stigsb/devais/docs/research/2026-09-13-mdbt50q.md

# Raytac MDBT50Q-1MV2 (nRF52840) — schematic research

Date: 2026-09-13. Every fact below is tagged VERIFIED (with source) or UNVERIFIED.

## Sources used

| Tag | Document | URL | Fetched |
|---|---|---|---|
| S1 | Raytac Approval Sheet, MDBT50Q-1MV2 & MDBT50Q-P1MV2, **Ver. L, 2023/05/24**, 73 pp (current version linked from Raytac's product page) | https://www.raytac.com/download/index.php?index_id=43 | yes (PDF downloaded, text + page images) |
| S2 | Same document, **Ver. K, 2022/07/01**, 75 pp (SparkFun mirror) | https://cdn.sparkfun.com/assets/4/7/4/3/8/_nRF52840__MDBT50Q-1MV2___MDBT50Q-P1MV2_Ver.K_spec.pdf | yes |
| S3 | Raytac product page MDBT50Q-1MV2 | https://www.raytac.com/product/ins.php?index_id=24 | yes |
| S4 | Nordic nRF52840 PS — Pin assignments | http://docs.nordicsemi.com/r/bundle/ps_nrf52840/page/pin.html | yes |
| S5 | Nordic nRF52840 PS — USBD | https://docs.nordicsemi.com/r/bundle/ps_nrf52840/page/usbd.html | yes |
| S6 | Nordic nRF52840 PS — SAADC | http://docs.nordicsemi.com/r/bundle/ps_nrf52840/page/saadc.html | yes |
| S7 | Nordic nRF52840 PS — UICR (REGOUT0) | http://docs.nordicsemi.com/r/bundle/ps_nrf52840/page/uicr.html | yes (enum values absent) |
| S8 | Nordic DevZone: "Resistors for D+ and D-?" | https://devzone.nordicsemi.com/f/nordic-q-a/94955/resistors-for-d-and-d- | yes |
| S9 | Nordic DevZone: "nRF52840 VDD output current maximum (Reg0 DCDC)" | https://devzone.nordicsemi.com/f/nordic-q-a/66975/nrf52840-vdd-output-current-maximum-reg0-dcdc | yes |
| S10 | Nordic DevZone: "nRF52840 Dongle Set REGOUT0 for 3V3 VDD OUT" | https://devzone.nordicsemi.com/f/nordic-q-a/84089/nrf52840-dongle-set-regout0-for-3v3-vdd-out | yes |
| S11 | Nordic SDK header `nrf52840_bitfields.h` (REGOUT0 enum), via sandeepmistry/arduino-nRF5 mirror of Nordic's SDK file | https://raw.githubusercontent.com/sandeepmistry/arduino-nRF5/master/cores/nRF5/SDK/components/device/nrf52840_bitfields.h | yes |
| S12 | Adafruit_nRF52_Bootloader repo | https://github.com/adafruit/Adafruit_nRF52_Bootloader | yes (via subagent) |

**Could not fetch:** Nordic PS `power.html` and `ref_circuitry.html` (WebFetch aborts: page exceeds 10 MB content limit). Nordic PS PDF direct download (`infocenter.nordicsemi.com/pdf/…`) returns HTTP 403. Mouser product pages (bot-detection block / 60 s timeout). Raytac "Footprint & Design Guide" ZIP (contains the recommended external 32.768 kHz spec) — not downloaded.

**Version note (VERIFIED, S1 vs S2):** I diffed the full §2.5 Pin Assignment text of Ver. K against Ver. L. They are byte-identical apart from page-number footers. The pad table below is current as of Ver. L.

---

## 1. Complete pad table — MDBT50Q-1MV2

VERIFIED, S1 §2.5 (pp. 14–17) / S2 §2.5 (pp. 16–18). 61 pads. Module 10.5 × 15.5 × 2.05 mm, 48 usable GPIO (S3).

**Legend:** `LF` = Raytac marks the pad "standard drive, low frequency I/O only". Raytac defines low-frequency I/O as **a signal with a frequency up to 10 kHz**, and states explicitly: **"SPI, I2C, UART, PWM are NOT low frequency I/O"** (S1 §2.6).

| Pad | Name | Function | Notes |
|---:|---|---|---|
| 1 | GND | Power | |
| 2 | GND | Power | |
| 3 | P1.10 | GPIO | **LF** |
| 4 | P1.11 | GPIO | **LF** |
| 5 | P1.12 | GPIO | **LF** |
| 6 | P1.13 | GPIO | **LF** |
| 7 | P1.14 | GPIO | **LF** |
| 8 | P1.15 | GPIO | **LF** |
| 9 | P0.03 / AIN1 | GPIO + analog in | **LF** |
| 10 | P0.29 / AIN5 | GPIO + analog in | **LF** |
| 11 | P0.02 / AIN0 | GPIO + analog in | **LF** |
| 12 | P0.31 / AIN7 | GPIO + analog in | **LF** |
| 13 | P0.28 / AIN4 | GPIO + analog in | **LF** |
| 14 | P0.30 / AIN6 | GPIO + analog in | **LF** |
| 15 | GND | Power | |
| 16 | P0.27 | GPIO | full-speed |
| 17 | P0.00 / XL1 | GPIO or 32.768 kHz crystal | |
| 18 | P0.01 / XL2 | GPIO or 32.768 kHz crystal | |
| 19 | P0.26 | GPIO | full-speed |
| 20 | P0.04 / AIN2 | GPIO + analog in | full-speed |
| 21 | P0.05 / AIN3 | GPIO + analog in | full-speed |
| 22 | P0.06 | GPIO | full-speed |
| 23 | P0.07 / TRACECLK | GPIO | full-speed |
| 24 | P0.08 | GPIO | full-speed |
| 25 | P1.08 | GPIO | full-speed |
| 26 | P1.09 / TRACEDATA3 | GPIO | full-speed |
| 27 | P0.11 / TRACEDATA2 | GPIO | full-speed |
| 28 | VDD | Power | supply in (normal mode) / REG0 output (high-voltage mode) |
| 29 | P0.12 / TRACEDATA1 | GPIO | full-speed |
| 30 | VDDH | Power | high-voltage supply |
| 31 | DCCH | Power | REG0 DC/DC converter output (external inductor) |
| 32 | VBUS | Power | 5 V input for the USB 3.3 V regulator |
| 33 | GND | Power | |
| 34 | D− | Digital I/O | USB D− |
| 35 | D+ | Digital I/O | USB D+ |
| 36 | P0.14 | GPIO | full-speed |
| 37 | P0.13 | GPIO | full-speed |
| 38 | P0.16 | GPIO | full-speed |
| 39 | P0.15 | GPIO | full-speed |
| 40 | P0.18 / nRESET | GPIO, configurable as system RESET | Raytac recommends QSPI/CSN |
| 41 | P0.17 | GPIO | full-speed |
| 42 | P0.19 | GPIO | Raytac recommends QSPI/SCK |
| 43 | P0.21 | GPIO | Raytac recommends QSPI |
| 44 | P0.20 | GPIO | full-speed |
| 45 | P0.23 | GPIO | Raytac recommends QSPI |
| 46 | P0.22 | GPIO | Raytac recommends QSPI |
| 47 | P1.00 / TRACEDATA0 | GPIO | Raytac recommends QSPI |
| 48 | P0.24 | GPIO | full-speed |
| 49 | P0.25 | GPIO | full-speed |
| 50 | P1.02 | GPIO | **LF** |
| 51 | SWDIO | Debug | SWD data |
| 52 | P0.09 / NFC1 | GPIO or NFC antenna | **LF** |
| 53 | SWDCLK | Debug | SWD clock |
| 54 | P0.10 / NFC2 | GPIO or NFC antenna | **LF** |
| 55 | GND | Power | |
| 56 | P1.04 | GPIO | **LF** |
| 57 | P1.06 | GPIO | **LF** |
| 58 | P1.07 | GPIO | **LF** |
| 59 | P1.05 | GPIO | **LF** |
| 60 | P1.03 | GPIO | **LF** |
| 61 | P1.01 | GPIO | **LF** |

### Raytac's LF list vs Nordic's LF list — they differ

- **Nordic** (VERIFIED, S4) marks exactly these aQFN73 pins "standard drive, low frequency I/O only": **P0.02, P0.03, P0.28, P0.29, P0.30, P0.31, P1.10, P1.11, P1.12, P1.13, P1.14, P1.15**. Same 10 kHz definition.
- **Raytac** (VERIFIED, S1 §2.5/§2.6) marks all of the above **plus P0.09, P0.10, P1.01, P1.02, P1.03, P1.04, P1.05, P1.06, P1.07**. §2.6 "GPIO Located Near the Radio" explains why: these sit next to the radio inside the module, and "wrong usage may lead to undesirable performance".

Treat Raytac's superset as binding for this module. Note that P1.08 and P1.09 (pads 25, 26) are **not** in either list, so they are full-speed on this module.

---

## 2. Review of the proposed pin allocation

**Result: every pad number is correct. Zero pad-number errors, zero non-GPIO pads, zero high-speed signals on low-frequency pads.**

| Signal | GPIO | Claimed pad | Pad table says | Verdict |
|---|---|---:|---|---|
| I2S BCLK | P0.26 | 19 | P0.26, full-speed | OK |
| I2S LRCLK | P0.27 | 16 | P0.27, full-speed | OK |
| I2S SDOUT | P0.08 | 24 | P0.08, full-speed | OK |
| PDM CLK | P0.06 | 22 | P0.06, full-speed | OK |
| PDM DATA | P0.07 | 23 | P0.07, full-speed | OK |
| PTT button | P0.02 | 11 | P0.02/AIN0, **LF** | OK — a button is DC, well under 10 kHz |
| PWR button | P0.03 | 9 | P0.03/AIN1, **LF** | OK — same |
| LED data (WS2812) | P0.11 | 27 | P0.11, full-speed | OK — 800 kHz needs a full-speed pad, and this is one |
| LED power enable | P0.12 | 29 | P0.12, full-speed | OK |
| Mic enable | P0.13 | 37 | P0.13, full-speed | OK |
| Amp enable | P0.14 | 36 | P0.14, full-speed | OK |
| Charger EN1 | P1.10 | 3 | P1.10, **LF** | OK — static enable |
| Charger EN2 | P1.11 | 4 | P1.11, **LF** | OK — static enable |
| Type-C status | P1.12 | 5 | P1.12, **LF** | OK if the signal is static/slow |
| Type-C status | P1.13 | 6 | P1.13, **LF** | OK if the signal is static/slow |
| Battery ADC | P0.04/AIN2 | 20 | P0.04/AIN2, full-speed | OK |
| RESET | P0.18 | 40 | P0.18/nRESET | OK |
| SWDIO | — | 51 | SWDIO | OK |
| SWDCLK | — | 53 | SWDCLK | OK |
| LF crystal XL1 | P0.00 | 17 | P0.00/XL1 | OK |
| LF crystal XL2 | P0.01 | 18 | P0.01/XL2 | OK |

### Issues that are not pad-number errors but affect the schematic

**A1 — Bootloader pin collision (VERIFIED, S12).** The stock Adafruit bootloader board `raytac_mdbt50q_db_40` (`UF2_BOARD_ID "nRF52840-MDBT50Q-1MV2"`) defines `BUTTON_DFU = P0.11` and `BUTTON_DFU_OTA = P0.12` — exactly your LED data and LED power-enable pins — and `LED_PRIMARY/SECONDARY/TERTIARY = P1.13/P1.14/P1.15`, of which P1.13 is your Type-C status pin. Using the stock board definition unmodified will fight your hardware at boot. Fork it into a custom board definition.

**A2 — P0.18 / nRESET is a plain GPIO on a blank part.** Pad 40 only behaves as a reset pin once UICR `PSELRESET[0]` and `PSELRESET[1]` are programmed to 18. Raised UICR bits need a page erase, i.e. SWD (see S10). Budget for that in the first flash.

**A3 — Battery ADC may be unnecessary.** If the design ends up in high-voltage mode (VDDH on the Li-ion rail), the SAADC `VDDHDIV5` input measures VDDH/5 internally with no external divider and no pin — freeing pad 20 (§6 below).

**A4 — Avoid the Raytac-only LF pads for anything fast.** P0.09, P0.10, P1.01–P1.07 and P1.02 are full-speed per Nordic but LF-only per Raytac. None are in your allocation; keep it that way.

**A5 — Unallocated but mandatory pads:** 1, 2, 15, 33, 55 (GND), 28 (VDD), 30 (VDDH), 31 (DCCH), 32 (VBUS), 34 (D−), 35 (D+). Covered in §3/§5.

---

## 3. USB pads and the normal-voltage-mode (VDD = VDDH = 3.3 V) reference circuit

Raytac §8.3 "Reg0 DC/DC and LDO Mode Disabled — Recommend using when the highest input voltage is less than 3.6 V" is the normal-voltage-mode circuit. VERIFIED, S1 p. 40 / S2 p. 42 (schematic image read at 400 dpi).

### Connections

| Pad | Net | Component |
|---:|---|---|
| 28 VDD | 3.3 V rail ("Normal Voltage input") | **C11 = 10 µF** to GND |
| 30 VDDH | **same 3.3 V rail** — tied directly to VDD | — |
| 31 DCCH | **not connected** | — |
| 32 VBUS | 5 V net | **C25 = 10 µF** to GND |
| 33, 15, 55, 1, 2 GND | GND | — |
| 34 D− | USB connector D− | **R30 = 27 Ω series** |
| 35 D+ | USB connector D+ | **R31 = 27 Ω series** |
| 17 XL1 / 18 XL2 | 32.768 kHz crystal X2 | **C12 = C13 = 12 pF**, marked *Optional* |
| 52 P0.09/NFC1, 54 P0.10/NFC2 | NFC loop | C19, C21 — **omit** if NFC unused |

Nordic confirms the mode: normal voltage mode is entered when the supply is connected to **both** VDD and VDDH (pins shorted); REG0 is then automatically bypassed and only REG1 runs.

### Series resistors on D+/D− — Raytac and Nordic disagree

- **Raytac (VERIFIED, S1 §8.3/§8.4):** shows **27 Ω in series on both D+ and D−** in every USB reference circuit.
- **Nordic (VERIFIED, S8):** Nordic employee, verbatim — *"The external series resistors are not required for D+ and D-. They are already built into the USB PHY."* A related thread notes the older DK's 39 Ω resistors were legacy and would be removed from future DKs.

Practical resolution: lay out **0 Ω / DNP-able footprints** on D+/D− so you can populate 0 Ω (Nordic-correct) and still fall back to Raytac's 27 Ω without a respin. Do not stack 27 Ω on top of the PHY's own series termination if you want a compliant eye.

### VBUS

- **5 V goes directly to pad 32.** No regulator, no divider. VBUS operating range **4.35 / 5.0 / 5.5 V** (min/nom/max); absolute max 5.8 V (VERIFIED, S1 §5.1/§5.2, reproduced from nRF52840 PS v1.7).
- The nRF52840 has a dedicated internal regulator converting VBUS to the 3.3 V used by the USB signalling interface, so **both VBUS and VDD (or VDDH) must be supplied for USB to work** (VERIFIED, S5).
- The **1.5 kΩ D+ pull-up is on-chip and software-controlled** (`USBPULLUP`). Nordic: *"This forbids the use of an external pull-up."* (VERIFIED, S5). Do not fit one.
- D+/D− are **not 5 V tolerant** (VERIFIED, S5). Nordic specifies no external components on them; ESD diodes are optional and your own call.
- Raytac's §8.5 "USB Disabled": **leave D+ and D− as NC** when USB is unused (VERIFIED, S1).
- Raytac's USB circuits show **C25 = 10 µF on VBUS**. UNVERIFIED whether Nordic mandates a specific VBUS cap value (the PS ref-circuitry page could not be fetched).

### Decoupling that Raytac requires

Raytac's reference circuits show only these external passives on the power pads (VERIFIED, S1 §8.1–§8.4):

- **VDD (pad 28): 10 µF (C11).** Present in every circuit.
- **VDDH (pad 30): 10 µF (C24).** Only in the high-voltage circuits; in normal mode VDDH is just tied to VDD and shares C11.
- **VBUS (pad 32): 10 µF (C25).**
- **DCCH (pad 31): 10 µH inductor (L4) to VDDH**, only when REG0 DC/DC is enabled. Raytac's spec: *"Recommended L4 spec: 10 µH, 0603 Chip Inductor, IDC,min = 80 mA, ±20%"*.
- **DEC1–DEC6 / DCC pins are not brought out** — they are inside the module and already decoupled. Nothing for you to fit.

Add your own 100 nF local bypass next to the module in addition to the bulk caps; Raytac does not show one but it costs nothing. (That last sentence is my recommendation, not a Raytac requirement.)

### What is already inside the module

VERIFIED, S1 §3 and the §8 preamble, verbatim: **"32 MHz crystal and RF (VDD) DC/DC inductor (Reg1) are already inside the module."** So:

- No external 32 MHz crystal or load caps.
- No external REG1 (DCC) inductor — the REG1 DC/DC inductor is internal, so `DCDCEN` can be enabled with no extra parts.
- The REG0 inductor (DCCH, L4) is **not** internal and must be added externally if you use REG0 DC/DC (high-voltage mode only).

Also VERIFIED (S1 §8 preamble), verbatim: *"Module is pre-programmed with Raytac testing code. Default is using LDO mode and need to add external 32.768 khz to work. You can use DC-DC mode without adding external 32.768 khz, they are NOT related events. When using internal 32.768 khz RC oscillator, please remove X2 / C12 / C13. When NOT using NFC, please remove NFC1 / C19 / C21."*

### External 32.768 kHz crystal

- **Pads: 17 (P0.00/XL1) and 18 (P0.01/XL2).** VERIFIED, S1 §2.5.
- **Raytac's reference circuit shows C12 = C13 = 12 pF** to GND, marked *Optional* (the crystal is only needed if you don't use the internal RC LFCLK). VERIFIED, S1 §8.1–§8.4.
- Raytac does **not** state a load-capacitance figure in the approval sheet. It says the recommended spec for the external 32.768 kHz is in the separate **Footprint & Design Guide** download (https://www.raytac.com/document/index.php?index_m_id=12). **UNVERIFIED — I did not download that package.** If you need a C_L number before ordering the crystal, pull that ZIP.
- Nordic's LFXO page states only *"To achieve correct oscillation frequency, the load capacitance must match the specification in the crystal data sheet"* and *"The load capacitors C1 and C2 should have the same value."* The numeric C_L / ESR table sits in the PS reference-circuitry section, which I could not fetch. **UNVERIFIED.**
- Note: the Adafruit bootloader hard-codes `NRF_CLOCK->LFCLKSRC = CLOCK_LFCLKSRC_SRC_RC` for **all** boards (VERIFIED, S12, `src/boards/boards.c`), so the bootloader itself never needs the crystal — only your application does.

---

## 4. Antenna keep-out and layout (VERIFIED, S1 §2.3, read from the 400 dpi page render)

Raytac's text, verbatim:

> "Make sure to keep the 'No Ground Pad' as wider as you can regardless of the size of your PCB."
> "No Ground Pad should be included in the corresponding position of the antenna in **EACH LAYER**."
> "Place the module towards the edge of PCB to have better performance than placing it on the center."

Dimensions from the keep-out drawing:

- **Copper-free strip: 3.8 mm deep**, measured from the module's antenna edge outward to the board edge.
- **Minimum width 10.5 mm** (the full module width), and Raytac says to widen it toward the full board width wherever possible. Their "NOT RECOMMENDED" examples show (a) ground poured right up to the antenna edge and (b) a keep-out only as wide as the module with ground on both sides — both rejected.
- The keep-out must be free of copper on **every layer**, top and bottom included.
- Module body 15.5 mm long × 10.5 mm wide, so with the keep-out the antenna end needs **3.8 mm of clear board** plus the module footprint.
- **Ground area:** pour solid ground under and around the rest of the module. Raytac's callout, verbatim: *"Please add via holes in GROUND area as many as possible, especially around the four corners."*
- Raytac offers a free layout review: PDF to service@raytac.com, subject "Layout reviewing – Raytac Model No. – YOUR company's name".

---

## 5. Availability, price, and bootloader

### Distributors

| Source | Part number | Stock | Price | Status |
|---|---|---|---|---|
| DigiKey Marketplace | **3271-MDBT50Q-1MV2-ND** | 14 | **$6.15 @ qty 1** | VERIFIED — https://www.digikey.com/en/products/detail/raytac/MDBT50Q-1MV2/13677591 . Marketplace listing fulfilled by Raytac: ~14-day ship, flat $25 shipping, no qty 10/100 breaks shown. |
| Mouser | — | — | — | **UNVERIFIED** — Mouser blocks automated fetches (bot-detection challenge / timeout). Search results confirm Mouser hosts the Raytac datasheet under its manufacturer folder, implying it carries the line, but no part number, stock, or price could be confirmed. Check https://www.mouser.com/c/?q=MDBT50Q-1MV2 manually. |
| LCSC | **C5118826** | **Out of stock** | $19.10 @ 1, $18.60 @ 10 | VERIFIED — https://www.lcsc.com/product-detail/C5118826.html . Package SMD-61P, 88/tray. |
| JLCPCB | **C5118826**, **Extended** part | **0 in stock, pre-order** | ~$18.97 (recent 2-pc order at $17.77/unit) | VERIFIED — https://jlcpcb.com/partdetail/RAYTAC-MDBT50Q1MV2/C5118826 . Assembly Type = SMT, PCBA Type = Economic and Standard, **X-ray inspection required**, MOQ 1, full reel 88. |

**JLCPCB can assemble it** — it is in the parts library as an Extended SMT part — but only as a pre-order with zero on-hand stock, and it carries an X-ray-inspection requirement (castellated module). Budget for Extended-part handling fees and pre-order lead time.

**Price discrepancy to note:** DigiKey $6.15 vs LCSC/JLCPCB ~$19. Raytac's own list price and Mouser's are unknown, so which figure is representative is **UNVERIFIED**. The 3× gap is worth a manual check before you commit to a sourcing plan.

**Raytac order codes (VERIFIED, S1 §4.3):** MDBT50Q-1MV2 → tray **MD-240A3-007**, tape & reel **MD-240A3-007R**. MOQ 1,500 pcs on reel, 88 pcs on tray.

### Adafruit nRF52 UF2 bootloader

VERIFIED, S12 (GitHub API + raw file fetches).

Two board definitions under `src/boards/` contain "mdbt50q":

1. **`raytac_mdbt50q_db_40`** — Raytac's MDBT50Q-DB-40 demo board, which carries an MDBT50Q-1MV2. `UF2_BOARD_ID = "nRF52840-MDBT50Q-1MV2"`. Pins: `LED_PRIMARY_PIN P1.13`, `LED_SECONDARY_PIN P1.14`, `LED_TERTIARY_PIN P1.15`, `BUTTON_DFU P0.11`, `BUTTON_DFU_OTA P0.12`, plus `BUTTON_3 P0.24`, `BUTTON_4 P0.25`. No `LED_NEOPIXEL`.
2. **`raytac_mdbt50q_rx`** — the MDBT50Q-RX USB dongle. `UF2_BOARD_ID = "nRF52840-MDBT50Q_RX-verD"`. `LEDS_NUMBER 1`, `LED_PRIMARY_PIN P1.13`, `BUTTON_DFU P0.15`, `BUTTON_DFU_OTA P0.10`. No `LED_NEOPIXEL`.

Neither overrides the LF clock; `src/boards/boards.c` hard-codes `NRF_CLOCK->LFCLKSRC = CLOCK_LFCLKSRC_SRC_RC` with the comment *"Use Internal OSC to compatible with all boards"*.

So: **yes, a board definition usable with a bare MDBT50Q exists** (`raytac_mdbt50q_db_40`), but its pin map collides with this project's allocation (see A1). Fork it.

Prebuilt release assets exist per board, e.g. `raytac_mdbt50q_db_40_bootloader-0.11.0_s140_6.1.1.hex`, `…zip`, and `update-raytac_mdbt50q_db_40_bootloader-0.11.0_nosd.uf2` (v0.11.0 and earlier releases).

### First bootloader flash requires SWD — CONFIRMED

VERIFIED, S12:

- Repo README: *"You must have have a J-Link available to 'unbrick' your device."*
- Makefile: `FLASHER ?= nrfjprog`; `make BOARD=<board> flash` runs `nrfjprog --program … --sectoranduicrerase -f nrf52 --reset` (J-Link over SWD). `make BOARD=<board> FLASHER=pyocd flash` runs `pyocd flash -t <mcu> …` (CMSIS-DAP over SWD).
- There is **no** `flash-jlink` or `flash-openocd` target, and OpenOCD is not referenced in the Makefile. Supported flashers are nrfjprog (J-Link) and pyOCD (CMSIS-DAP or J-Link). OpenOCD would work electrically over SWD but is not a supported make target — **UNVERIFIED** as an official path.
- `flash-uf2` / `flash-dfu` targets only work once a bootloader is already resident, so they are useless on a factory-blank part.
- Raytac ships bare modules with **factory test code, no bootloader** (VERIFIED, S1 §8 preamble). Raytac's own catalog lists no bootloader-preloaded MDBT50Q SKU; the UF2 bootloader on Adafruit's MDBT50Q-RX (product #5199) is an Adafruit-added customization — **UNVERIFIED** whether Raytac offers that to other customers.

**Conclusion:** wire SWDIO (pad 51), SWDCLK (pad 53), GND and VDD to a programming header. First flash must go over SWD via a J-Link (nrfjprog) or a CMSIS-DAP probe (pyOCD). Setting `PSELRESET` and `REGOUT0` in UICR also requires SWD, for the same page-erase reason (S10).

---

## 6. High-voltage mode (VDDH on the Li-ion rail) and battery sensing

### (a) High-voltage mode

**VDDH operating range: 2.5 V min / 3.7 V nom / 5.5 V max** (VERIFIED, S1 §5.2, reproduced from nRF52840 PS v1.7). Absolute max 5.8 V (§5.1). A 2.9–4.4 V Li-ion system rail sits inside that window with margin at both ends.

Additional constraint (VERIFIED, S9 — Nordic DevZone): **VDDH must stay more than 0.3 V above VDD, or REG0 cannot regulate.** With REGOUT0 = 3.0 V and a Li-ion cell that reaches 3.0 V near empty, REG0 drops out of regulation at the bottom of the discharge curve. Pick REGOUT0 ≤ 2.7 V if you need regulation down to a 2.9 V cell, or accept that VDD sags with the cell below ~3.3 V.

**REGOUT0 (UICR 0x304) selectable REG0 outputs** (VERIFIED, S11 — Nordic SDK `nrf52840_bitfields.h`; the enum is absent from the fetchable docs page S7):

| Value | Voltage |
|---:|---|
| 0 | 1.8 V |
| 1 | 2.1 V |
| 2 | 2.4 V |
| 3 | 2.7 V |
| 4 | 3.0 V |
| 5 | 3.3 V |
| 7 | DEFAULT = 1.8 V (erased UICR) |

Nordic's own wording for the register (S7): *"Output voltage from REG0 regulator stage. The maximum output voltage from this stage is given as VDDH − V_VDDH-VDD."*

**On a blank device REGOUT0 reads 0xFFFFFFFF → 1.8 V.** All GPIOs then run at 1.8 V logic. You must program REGOUT0 over SWD before your 3.3 V-logic peripherals will work. Raising the field (e.g. 3V0 = 0b100 → 3V3 = 0b101) turns a 0 into a 1 and therefore needs a **UICR page erase, only possible with a debugger** (VERIFIED, S10, Nordic employee). Plan the production flow so REGOUT0 is set once at the same time as the bootloader.

**Maximum external load from the VDD pad in high-voltage mode: 25 mA**, valid when radio output power is ≤ 4 dBm (VERIFIED, S9 — Nordic employee Robin M Saltnes; this is the external draw from VDD, not the chip's own consumption). A ~1 mA PDM microphone is 4 % of that budget — comfortably fine. The thread does not cite a PS table number, so treat 25 mA as an engineering-support figure rather than a datasheet line; **the PS table it derives from is UNVERIFIED** (PS `power.html` and `ref_circuitry.html` exceed the fetch size limit).

**Raytac does document high-voltage-mode reference circuits for MDBT50Q-1MV2** — two of them (VERIFIED, S1 §8.1 p. 36 and §8.2 p. 38, both headed *"Recommend using when the highest input voltage is equal or greater than 3.6 V. Supply power from VDDH."*):

§8.1 — REG0 DC/DC enabled:

| Pad | Connection |
|---:|---|
| 30 VDDH | Li-ion rail ("High Voltage input"), **C24 = 10 µF** to GND |
| 31 DCCH | **L4 = 10 µH** to the VDDH rail (0603, I_DC,min 80 mA, ±20 %) |
| 28 VDD | **C11 = 10 µF** to GND — VDD is an *output* here, nothing else drives it |
| 32 VBUS | 5 V net, **C25 = 10 µF** to GND |
| 34/35 D−/D+ | 27 Ω series to the USB connector, same as normal mode |

§8.2 — REG0 LDO mode: identical except **DCCH (pad 31) is left unconnected and L4 is omitted**.

So the extra part count for high-voltage mode over normal mode is: one 10 µF on VDDH, and (DC/DC only) one 10 µH inductor. VDD keeps its own 10 µF and must **not** be tied to VDDH.

**USB works in high-voltage mode — confirmed.** Both Raytac high-voltage circuits carry VBUS + D+/D− (VERIFIED, S1). Nordic's own nRF52840 Dongle **PCA10059 does exactly this**: VDDH from USB 5 V, `L4 10 µH` between DCCH and VDD per the PS high-voltage DC/DC configuration, USB enumerating normally, and newer dongles ship with REGOUT0 already set to 3.0 V (0x4) (VERIFIED, S10). The USB PHY runs off its own VBUS-fed regulator, so it does not care which REG0 mode the rest of the chip is in.

### (b) SAADC VDDHDIV5

**VERIFIED, S6 (nRF52840 PS SAADC chapter).** The SAADC input selection includes **AIN0–AIN7, VDD, and VDDHDIV5**. VDDHDIV5 presents VDDH/5 to the ADC, so battery voltage is readable with **no external divider and no pin consumed**.

Stated constraint (VERIFIED, S6, verbatim): *"when using VDDHDIV5 as input, the acquisition time must be 10 µs or longer."* Set `CH[n].CONFIG.TACQ` to ≥ 10 µs.

Accuracy: the PS SAADC page I fetched gives no dedicated VDDHDIV5 accuracy figure. **UNVERIFIED** figures circulating on DevZone: divider ±1 %, internal 0.6 V reference ±3 %. Treat those as community numbers, not datasheet numbers — the PS electrical-spec tables sit in sections I could not fetch. Practical note from the same threads (also UNVERIFIED): sample VDDH during a peak-current moment, otherwise you read the unloaded cell voltage.

Also relevant: errata PAN 160 recorded VDDHDIV5 as non-functional on engineering silicon rev. Engineering A (QIAA-AA0). Raytac ships rev. 2 IC on modules with date code 914 and later, identified by the **absence** of a black dot on the shield (VERIFIED, S1 §4). Modules with one black dot are revision 1.

---

## Open items / not verified

1. **Mouser stock and price** — bot-blocked. Needs a manual check.
2. **Raytac's recommended external 32.768 kHz crystal spec** (load capacitance, ESR) — lives in the separate Footprint & Design Guide ZIP at https://www.raytac.com/document/index.php?index_m_id=12, not downloaded.
3. **Nordic's LFXO numeric C_L / ESR table** and **the full aQFN73 reference-circuit BOM** — `docs.nordicsemi.com` `power.html` and `ref_circuitry.html` exceed the 10 MB fetch limit; the PS PDF returns HTTP 403 from infocenter.
4. **The PS table backing the 25 mA REG0 external-load figure** — the number comes from a Nordic employee on DevZone, not from a page I could read directly.
5. **VDDHDIV5 accuracy numbers** (±1 % divider, ±3 % reference) — DevZone community figures, not confirmed against the PS electrical-spec tables.
6. **Whether Nordic mandates a specific VBUS capacitor value** — Raytac shows 10 µF; Nordic's ref-circuitry page unreadable.
7. **OpenOCD as a supported bootloader-flash path** — electrically fine over SWD, but the repo provides no make target for it.
8. **Whether Raytac sells a UF2-bootloader-preloaded MDBT50Q SKU** — none found in Raytac's catalog; the Adafruit MDBT50Q-RX bootloader appears to be an Adafruit-specific customization.
9. **DigiKey $6.15 vs LCSC/JLCPCB ~$19** — unexplained 3× gap; which is representative is unknown.

---

## 7. Pad physical form: castellated vs underside — and pitch

Source: Raytac approval sheet §2.1 "PCB Dimensions & Pin Indication" (p. 7) and §2.2 "Recommended Layout of Solder Pad" (pp. 9–12), Ver. K; identical drawings in Ver. L. I rendered these pages at 600 dpi and machine-extracted all 61 pad rectangles, then cross-checked the result against the dimensioned land pattern on p. 12.

### Headline: the premise of "all castellated" does not hold

**VERIFIED (Raytac §2.2 p. 12, dimensioned land pattern):** the land pattern is a **staggered two-row array on three sides plus a free-standing mid-board row**, and **no land reaches the module outline**. Origin (0,0) is the bottom-left corner of the 10.5 × 15.5 mm outline; the nearest land centres sit at x = 0.45–0.6 mm and y = 0.6 mm, with a 0.6 mm land length. The outer row therefore stops roughly 0.15 mm short of the edge.

**VERIFIED (grep of the full Ver. K and Ver. L text):** the approval sheet never uses the words "castellated", "half-hole", "LGA" or "hand solder" anywhere.

**Conclusion (VERIFIED by drawing geometry; UNVERIFIED as an explicit Raytac statement):** this is a **bottom-terminated LGA-style module, not a castellated one**. A castellated module's recommended land pattern always extends the land *outside* the body outline so a side fillet can form; Raytac's does the opposite. Corroborating but circumstantial: JLCPCB flags this part **"X-ray inspection required"**, which is what you would expect for hidden bottom terminations.

**Practical consequence: plan for reflow (stencil + paste + oven or hotplate). Do not plan to tack it down with a soldering iron from the side.** If you need iron-solderable side access, use a carrier/breakout board rather than this module direct-mounted.

**Caveat:** the definitive artefact is the 2D/3D drawing inside Raytac's Footprint & Design Guide package (https://www.raytac.com/document/index.php?index_m_id=12), which I did not download. If the iron-solderability question is load-bearing for your assembly plan, open that package — or ask Raytac directly — before committing.

### Pad geometry (all VERIFIED, §2.2 pp. 11–12)

- **All 61 lands are 0.6 × 0.4 mm** — the drawing is annotated verbatim `61 pad_0.6x0.4`. There are **61 lands and nothing else**: no central thermal pad, no ground slug. The middle of the footprint is empty apart from the six-land mid-board row.
- **Pitch within a row: 0.8 mm.**
- **Pitch between consecutive pad *numbers*: 0.4 mm**, because numbering alternates between the outer and inner row. This is the number that governs your fab's capability.
- **Row-to-row spacing: 0.9 mm** (outer row at 0.6 mm from the edge datum, inner row at 1.5 mm; on the right side 9.9 mm and 9.0 mm).
- Keep-out annotations on the same drawings: **"No ground pad" 12.4 mm wide × 3.8 mm deep** at the antenna end (matching §2.3), plus a small **"Toplayer no ground pad" 1.6 × 1.2 mm** window located 2.95 mm in from the left edge, just below the antenna keep-out.

### Which pads are on the outer (edge-adjacent) row vs underside-only

Derived from the measured land coordinates on p. 12. Even on the outer row these are bottom-face lands — "outer" here means edge-adjacent, i.e. the row that *would* be castellated on a castellated module and the row that gets whatever limited visual/iron access exists.

**Outer, edge-adjacent row — 33 pads:**

| Side | Pad numbers |
|---|---|
| Left (x = 0.6) | 1, 2, 3, 4, 6, 8, 10, 12, 14 |
| Bottom (y = 0.6) | 15, 16, 17, 18, 20, 22, 24, 26, 28, 30, 31, 32, 33 |
| Right (x = 9.9) | 34, 35, 37, 39, 41, 44, 46, 48, 51, 53, 55 |

**Inner / underside-only — 28 pads:**

| Group | Pad numbers |
|---|---|
| Left inner row (x = 1.5) | 5, 7, 9, 11, 13 |
| Bottom inner row (y = 1.5) | 19, 21, 23, 25, 27, 29 |
| Right inner row (x = 9.0) | 36, 38, 40, 42, 43, 45, 47, 49, 50, 52, 54 |
| Mid-board row (y = 7.2, x = 3.25/4.05/4.85/5.65/6.45/7.25) | 56, 57, 58, 59, 60, 61 |

33 + 28 = 61. ✓

The **mid-board row (56–61 = P1.04, P1.06, P1.07, P1.05, P1.03, P1.01)** is the unambiguous case: it sits in the middle of the module underside, 7.2 mm up from the bottom edge and 3.25–7.25 mm in from the left, with no edge anywhere near it. Those six are reflow-only under any reading of the drawing.

Note the numbering is not a clean odd/even alternation, because the array has gaps: on the right side the positions at y = 8.8, 5.6 and 2.0 mm are empty, which shifts the parity. Pads 49/50 are both inner, 42/43 are both inner, and 34/35 are both outer. Read the table above rather than assuming a rule.

### Bearing on the current pin allocation

Of the proposed signals, these land on **underside-only** pads: **PTT P0.02 (pad 11)**, **PWR button P0.03 (pad 9)**, **Type-C status P1.13 (pad 6 — outer, fine)**. Checking each: pad 9 → inner, pad 11 → inner. Pads 3, 4, 5, 6 (charger EN1/EN2, Type-C status) are all outer. Pads 16, 19, 20, 22, 23, 24, 27, 29 — of these **19, 27, 29 are inner**, so **I2S BCLK (pad 19), LED data (pad 27) and LED power enable (pad 29) are underside-only**. Pads 36, 37, 40, 51, 53 → 36 is inner, 37/39-adjacent 37 is outer, 40 is inner, 51 and 53 are outer.

Summarised — underside-only signals in the current allocation: **PWR button (9), PTT (11), I2S BCLK (19), LED data (27), LED power enable (29), amp enable (36), RESET (40)**. Edge-adjacent: charger EN1/EN2 (3, 4), Type-C status (5, 6), I2S LRCLK (16), XL1/XL2 (17, 18), battery ADC (20), PDM CLK (22), PDM DATA (23), I2S SDOUT (24), mic enable (37), SWDIO (51), SWDCLK (53).

Useful consequence: **SWDIO, SWDCLK and both crystal pads are on the outer row**, so the debug and LFXO connections are the most accessible ones for rework and probing.
