stigsb/devais/docs/research/2026-09-13-pdm-mic.md

# PDM MEMS microphone for nRF52840 — LCSC/JLCPCB stock survey

Date of stock/price data: **2026-09-13**. All stock and price figures are live-page reads and go stale fast.

## Recommendation

**TDK InvenSense T3902, order code `MMICT390200012`, LCSC/JLCPCB `C3171752`.**
Bottom port, PDM, 3.5 x 2.65 x 0.98 mm, 1.65–3.63 V, Standard Mode clock **1.0–3.3 MHz** (covers
every nRF52840 Ratio64 clock option), 8,456 in stock, JLCPCB Extended, $1.289 @10.

**Fallback: MEMSensing MSM261DDB019, LCSC `C51928210`** — same footprint and pinout order,
cheaper, but its usable clock band is 1.1–4.8 MHz, so the nRF must run at 1.280 MHz with
`RATIO=Ratio80`, not the 1.032 MHz default.

---

## 1. nRF52840 PDM clock — VERIFIED

Source: nRF52840 Product Specification, PDM chapter, `PDMCLKCTRL.FREQ`
(https://docs.nordicsemi.com/r/bundle/ps_nrf52840/page/pdm.html) — VERIFIED.

| Enum | Value | PDM_CLK | Note in PS |
|---|---|---|---|
| 1000K | 0x08000000 | 32 MHz / 32 = 1.000 MHz | |
| Default | 0x08400000 | 32 MHz / 31 = 1.032 MHz | Nominal clock for RATIO=Ratio64 |
| 1067K | 0x08800000 | 32 MHz / 30 = 1.067 MHz | |
| 1231K | 0x09800000 | 32 MHz / 26 = 1.231 MHz | |
| 1280K | 0x0A000000 | 32 MHz / 25 = 1.280 MHz | Nominal clock for RATIO=Ratio80 |
| 1333K | 0x0A800000 | 32 MHz / 24 = 1.333 MHz | |

**Correction to the brief's premise.** The nRF52840 is *not* limited to 1.000/1.032/1.067 MHz.
`RATIO` selects Ratio64 or Ratio80, and PDMCLKCTRL offers 1.231/1.280/1.333 MHz for the Ratio80
family. 1.032 MHz / 64 = 16.125 kHz; 1.280 MHz / 80 = 16.0 kHz. Both give ~16 kHz voice audio.
This matters: several in-stock mics have a 1.1 or 1.2 MHz minimum clock and are unusable at
1.032 MHz but fine at 1.280 MHz.

Also VERIFIED from the same chapter: PDM clock jitter ~20 ns, duty cycle 40–60 %; the electrical
spec table names fPDM,CLK,64 = 1.032 MHz and fPDM,CLK,80 = 1.280 MHz.

---

## 2. Candidates ruled out at LCSC (all VERIFIED on live LCSC pages, 2026-09-13)

| Part | LCSC | Status |
|---|---|---|
| Infineon IM69D130V01XTSA1 | C42464166 | "Not available now / Not recommended for new" |
| Infineon IM72D128VV01XTMA1 | C36405960 | 0 in stock |
| Knowles SPH0641LM4H-1 / SPH0641LU4H-1 / SPK0641 | — | 0 search results — LCSC no longer lists any SPH0641 |
| ST MP34DT05-A / MP34DT06J / MP34DB02 / MP23DB01HP | — | 0 search results for "MP34DT", "MP34DT06JTR" |
| TDK T5848 (MMICT5848-00-012) | C20344623 | "Not available now" |
| MEMSensing MSM261DDB020 | C27636198 | "Not available now" (5,024 via 3rd-party, 5–7 day lead, 160 pc MOQ) |
| MEMSensing MSM261D4030H1CPM | C966942 | "Not available now / Not recommended for new" |
| MEMSensing MSM261D3526H1CPM (XIAO Sense mic) | — | 0 search results |
| ZILLTEK ZTS6216 | C481302 | LCSC page 404 "Part not found" (still listed in JLCPCB's cached parts index) |
| TDK ICS-43434 | C5656610 | 3,147 in stock but **I2S, not PDM** — out of scope |

Note: JLCPCB's MEMS-microphone category index page still shows rows for SPH0641LM4H-1 (C497724),
MP34DT06JTR (C503097) and IM69D130V01 (C536262). Those JLCPCB part pages render, but the
corresponding LCSC product pages are gone, and JLCPCB shows no stock figure for them. Treat the
JLCPCB index numbers as stale — UNVERIFIED as purchasable.

---

## 3. Viable in-stock candidates

### 3.1 TDK InvenSense T3902 — `MMICT390200012` — LCSC/JLCPCB `C3171752`  ← RECOMMENDED

Datasheet DS-000357 rev 1.0, "T3902 Bottom Port PDM Low-Power Multi-Mode Microphone With High
AOP Mode" (via https://www.lcsc.com/datasheet/C3171752.pdf) — VERIFIED.

| Item | Value | Source |
|---|---|---|
| Stock (LCSC) | 8,456 | LCSC product page — VERIFIED |
| Stock (JLCPCB) | 8,456; available order qty 7,938 | jlcpcb.com/partdetail/C3171752 — VERIFIED |
| Price @10 | $1.298 (LCSC) / $1.2890 (JLCPCB) | VERIFIED |
| JLCPCB library | **Extended**, SMT Assembly, PCBA type Economic **and** Standard, assembly difficulty "High", MSL 1 | VERIFIED |
| Port | **Bottom port** | datasheet title/description — VERIFIED |
| Package | LGA-5, 3.50 x 2.65 x 0.98 mm; sound port Ø0.375 mm | VERIFIED |
| Supply | 1.65–3.63 V | Table 1 — VERIFIED |
| Clock, Sleep | ≤ 200 kHz, 12 µA typ / 20 µA max | Table 1, Table 6 — VERIFIED |
| Clock, Low-Power | 400–800 kHz, 185 µA, SNR 63 dBA (8 kHz BW), AOP 120 dB SPL | Table 4/6 — VERIFIED |
| Clock, **Standard** | **1.0–3.3 MHz**, 430 µA typ / 500 µA max, SNR **64.5 dBA**, AOP **120 dB SPL**, sens −26 dBFS | Table 3/6 — VERIFIED |
| Clock, High-Perf | 4.1–4.8 MHz, 650 µA, SNR 64 dBA, AOP 126 dB SPL, sens −32 dBFS | Table 2/6 — VERIFIED |
| Clock duty cycle | 40–60 % below 3.3 MHz (nRF is 40–60 %) | Table 6 — VERIFIED |
| LF −3 dB | 36 Hz | VERIFIED |
| Latency | < 30 µs; wake from sleep < 20 ms; start-up < 20 ms | VERIFIED |
| Pinout | 1 DATA, 2 SELECT (L/R), 3 GND, 4 CLK, 5 VDD | Table 9 — VERIFIED |
| SELECT | GND = right channel, data driven on CLK **falling** edge; VDD = left channel, driven on rising edge | Table 10 + Fig 1 — VERIFIED |
| Decoupling | 0.1 µF X7R ceramic between pin 5 and GND, as close to pin 5 as layout allows | pin table + applications — VERIFIED |
| PCB sound hole | not smaller than the 0.375 mm package port; **0.5–1.0 mm diameter recommended**; align with package port; keep solder paste off the hole | PCB Design and Land Pattern Layout — VERIFIED |
| Land pattern | 1:1 with package pads; datasheet gives Ø1.025 inner / Ø1.625 outer hole rings and 0.522 x 0.725 mm pads (x4) | VERIFIED |
| Other layout rules | no pull-up/pull-down on DATA (it tristates); no buffer needed for short traces (<15 cm) | VERIFIED |

Sleep behaviour detail worth knowing for a push-to-talk design: with CLK stopped and SELECT tied
to GND, DATA goes high-impedance; with SELECT tied to VDD, DATA is pulled to GND. Either is safe;
tying SELECT low keeps the nRF PDM DIN pin floating when idle, so enable the nRF's internal
pull-down or accept the float. VERIFIED from the Sleep Mode section.

Why it wins: it is the only in-stock bottom-port PDM part whose normal (Standard) mode starts at
**1.0 MHz**, so it runs directly at the nRF52840 reset-default 1.032 MHz with RATIO=Ratio64 —
no clock re-plan, and the same part also covers 1.280/Ratio80 if you prefer exactly 16 kHz.
It additionally gives a genuine 400–800 kHz Low-Power always-on mode at 185 µA, which the
nRF cannot clock directly from PDMCLKCTRL but which is reachable with a PWM/timer-driven clock
if a wake-word path is ever added.

Drawback: ~$1.29 @10 is the most expensive of the viable set, and the Infineon-class 69–71 dB
SNR is not on offer here (64.5 dBA).

### 3.2 MEMSensing MSM261DDB019 — LCSC/JLCPCB `C51928210`  ← FALLBACK

Datasheet DS-042 v1.2 Aug 2023 (via https://www.lcsc.com/datasheet/C51928210.pdf) — VERIFIED.

| Item | Value |
|---|---|
| Stock | LCSC 1,830 / JLCPCB 1,830 (order qty 1,785) — VERIFIED |
| Price @10 | $0.5688 (LCSC) / $0.5713 (JLCPCB) — VERIFIED |
| JLCPCB library | **Extended**, SMT Assembly, Economic and Standard — VERIFIED |
| Port | **Bottom port** — VERIFIED ("omnidirectional, Bottom-ported, PDM digital output") |
| Package | LGA-5 metal can, 3.50 x 2.65 x 0.98 mm; acoustic port Ø0.325 ±0.05 mm — VERIFIED |
| Supply | 1.6–3.6 V (abs max 4.0 V) — VERIFIED |
| Sleep | fCLK ≤ 50 kHz, 1 µA typ; fall-asleep ≤ 30 µs; wake-up ≤ 20 ms — VERIFIED |
| Low-Power | fCLK 150–900 kHz, 320 µA, SNR 65 dB(A) 20 Hz–8 kHz — VERIFIED |
| **Standard** | **fCLK 1.1–4.8 MHz**, 750 µA, SNR **66 dB(A)**, sens −26 dBFS, **AOP 120 dB SPL**, THD 0.1 % — VERIFIED |
| Clock duty cycle | 40–60 % — VERIFIED |
| Pinout | 1 DATA, 2 L/R, 3 GND, 4 CLK, 5 VDD — VERIFIED |
| L/R | L/R = VDD → data on CLK rising edge; L/R = GND → data on falling edge — VERIFIED |
| PCB sound hole | not stated in the datasheet — UNVERIFIED. Use the same rule as T3902: ≥ package port (0.325 mm), 0.5–1.0 mm is safe |
| Decoupling | not stated explicitly — UNVERIFIED; 0.1 µF X7R at VDD is the standard practice for this class |

**Clock caveat (the reason this is the fallback, not the pick).** 900 kHz–1.1 MHz is a dead band
for this part. The nRF's 1.000/1.032/1.067 MHz options all land in that gap. Usable nRF settings
are therefore `PDMCLKCTRL=1280K` with `RATIO=Ratio80` (16.000 kHz) or `1231K`/`1333K` with
Ratio80 (15.39 / 16.66 kHz). 1.280 MHz / Ratio80 is the clean choice.

Upsides over the T3902: 66 dB(A) SNR (1.5 dB better), less than half the price, 1 µA sleep
instead of 12 µA, and a wider 1.6 V supply floor. Downside: only 1,830 in stock and a
second-tier vendor.

### 3.3 Other in-stock parts examined, not recommended

| Part | LCSC | Stock | $@10 | Port | Clock (normal) | Why not |
|---|---|---|---|---|---|---|
| MEMSensing MSM261DCB002 | C51928216 | 507 | $0.5615 | bottom (VERIFIED) | 1.1–4.8 MHz | Smallest package (2.75 x 1.85 x 0.9 mm, port Ø0.325) and 64 dB(A) SNR, but only 507 in stock and same 1.1 MHz floor. Pinout 1 VDD, 2 CLK, 3 GND, 4 L/R, 5 DATA — note this differs from DDB019. |
| MEMSensing MSM261DGT003 | C48227730 | 4,848 | $0.7273 | **top** (VERIFIED) | 1.1–4.0 MHz | Top port; 4.0 x 2.0 x 1.1 mm, port Ø0.65. 64 dB(A), 670 µA. Only if a top-port design is chosen. |
| MEMSensing MSM261DHP006 | C22390138 | 2,713 | $0.5749 | **top** (VERIFIED) | 1.1–4.8 MHz | Top port, 4 x 3 x 1.0 mm, 64 dB(A), AOP 120. |
| MEMSensing MSM261DHT006 | C51928215 | 3,297 | $0.4474 | **top** (VERIFIED) | 1.1–4.8 MHz | Top port, 4 x 3 x 1.05 mm, only 60 dB(A) SNR. |
| Goertek SD18OB261-060 | C2895290 | 6,331 | $0.7932 | bottom — **UNVERIFIED** (drawing implies bottom, text never says) | **1.2–3.5 MHz** | Highest clock floor of the set; 1.2 MHz excludes 1.000/1.032/1.067/1.231 MHz, leaving only 1.280/1.333 MHz. Supply 1.60–3.6 V, SNR 65 dB, AOP 120, 500 µA, sleep < 150 kHz at 10 µA, pinout 1 DATA / 2 L/R / 3 GND / 4 CLK / 5 VDD, package 3.50 x 2.65 x 0.98, port Ø0.325. Also has no low-power mode. |

All five fit a 15 x 8 mm daughterboard comfortably.

---

## 4. Board notes for the recommended part

- Footprint: LGA-5(3.5x2.7) — EasyEDA/JLCPCB library symbol + footprint exist for C3171752 (VERIFIED
  on the JLCPCB part page), so the JLCPCB footprint can be imported rather than hand-drawn.
- Sound hole in the daughterboard: **0.8 mm** is a good middle of the 0.5–1.0 mm recommended range —
  comfortably above the 0.375 mm package port and still small enough to keep a gasket seal simple.
  It faces the enclosure's 1.5 mm acoustic hole; leave the mic's own port unobstructed and keep
  the acoustic path short.
- Solder paste: mask the sound hole out of the stencil (no paste on or in the hole).
- Decoupling: 0.1 µF X7R 0402 from VDD (pin 5) to GND, placed against pin 5.
- SELECT (pin 2): tie to GND for right channel / data on CLK falling edge. Keep it a hard tie, not
  a floating net.
- CLK and DATA: no series termination or pull resistors needed at this trace length. Do not add a
  pull-up/pull-down on DATA.
- Assembly: JLCPCB tags this part "assembly difficulty: High" and it is MSL 1, which is the easy end
  for moisture. Expect the usual MEMS-mic caveats: no board wash after reflow, limited reflow cycles.

## 5. Open / unverified items

- Goertek SD18OB261-060 port orientation (top vs bottom) — UNVERIFIED from the datasheet text.
- MSM261DDB019 recommended PCB sound-hole diameter and decoupling — not in its datasheet; the
  figures above are carried over from the T3902 application notes as a reasonable default.
- JLCPCB's parts-index rows for SPH0641LM4H-1 / MP34DT06JTR / IM69D130V01 show stock figures but
  the matching LCSC products are delisted — UNVERIFIED whether JLCPCB can still source them.
- JLCPCB stock is checked at order time; 8,456 today does not guarantee availability at fab time.
  For a one-off prototype run, add the part to a JLCPCB parts library early.

## 6. Sources

- nRF52840 Product Specification, PDM chapter: https://docs.nordicsemi.com/r/bundle/ps_nrf52840/page/pdm.html
- LCSC C3171752: https://www.lcsc.com/product-detail/C3171752.html — datasheet https://www.lcsc.com/datasheet/C3171752.pdf (TDK DS-000357)
- JLCPCB C3171752: https://jlcpcb.com/partdetail/C3171752
- LCSC C51928210: https://www.lcsc.com/product-detail/C51928210.html — datasheet https://www.lcsc.com/datasheet/C51928210.pdf (MEMSensing DS-042 v1.2)
- JLCPCB C51928210: https://jlcpcb.com/partdetail/C51928210
- LCSC C2895290 (Goertek): https://www.lcsc.com/product-detail/C2895290.html
- LCSC microphone category: https://www.lcsc.com/category/54.html
