stigsb/devais/docs/research/2026-09-13-sh-cables.md

# Ready-made 1.0 mm pitch SH-compatible double-ended cable assemblies

Research date: 2026-09-13. Every fact tagged VERIFIED (with source URL) or UNVERIFIED.

## F1. The key enabling fact: JST SR (IDC) housings mate with SH headers

There is **no JST catalog harness built from SH crimp housings (SHR-xxV-S-B) on both ends**.
JST's finished double-ended 1.0 mm catalog harness uses the **SR** series IDC housing
(`xxSR-3S`), which mates with the **same headers** as the SH crimp housing.

- VERIFIED — JST SH datasheet, feature list: "Socket compatible with IDC style SR connector".
  https://www.jst-mfg.com/product/pdf/eng/eSH.pdf
- VERIFIED — JST SR/SZ product page: "Compatible Crimp-style connector available (SH connector)".
  https://www.jst-mfg.com/product/detail_e.php?series=244
- VERIFIED — DigiKey JST product highlight: "The SR series IDC housings can mate with the SH series headers."
  https://www.digikey.com/en/product-highlight/j/jst/sh-and-sr-series-connectors

So if the board footprints are standard SH headers (`SM0xB-SRSS-TB` side-entry or
`BM0xB-SRSS-TB` top-entry), the JST `AxxSRxxSR30K…` harness plugs straight in.

### Consequences vs. an SH crimp harness
| | SH crimp (SHR-xxV-S-B + SSH-003T-P0.2-H) | SR IDC (xxSR-3S, catalog harness) |
|---|---|---|
| Current rating | 1.0 A AC/DC (AWG #28) — VERIFIED, eSH.pdf | 0.7 A AC/DC — VERIFIED, eSR_SZ.pdf |
| Wire | AWG #32–#28, insulation OD 0.4–0.8 mm — VERIFIED, eSH.pdf | AWG #30 only, 7 strands tin-coated annealed copper, insulation OD 0.54–0.58 mm — VERIFIED, eSR_SZ.pdf |
| Voltage | 50 V | 50 V — VERIFIED |
| Temp | −25 to +85 °C | −25 to +85 °C — VERIFIED |

0.7 A per contact is the only downgrade. For the 8-pin USB harness with VBUS and GND
doubled up (2 contacts each), that is 1.4 A of headroom — adequate.

## F2. Part number scheme (confirmed)

`A` + NN + `SR` + NN + `SR` + `30` + `K` + LLL + `A`/`B`

- `A` — assembly prefix
- first `NN SR` — positions + housing series, end 1
- second `NN SR` — positions + housing series, end 2
- `30` — wire gauge, AWG 30 (UL1571, black) — VERIFIED on JST drawings GAM-286/GAM-287
- `K` — separator
- `LLL` — wire length in mm: `51` (2"), `102` (4"), `152` (6"), `203` (8"), `254` (10"), `305` (12") — VERIFIED, all six exist on DigiKey for 2/4/7/8 positions
- trailing letter — pin-out, see F3

Housings used are `02SR-3S`, `04SR-3S`, `07SR-3S`, `08SR-3S` (VERIFIED, GAM-286/287 Table 1).
`08SR-3S` alone is $0.53 at DigiKey, "CONN RCPT 8POS IDC 30AWG TIN" (VERIFIED,
https://www.digikey.com/en/products/result?keywords=08SR-3S).

## F3. ORIENTATION — DigiKey's label is the opposite of JST's pin-out. Read carefully.

From the JST manufacturing drawings (primary source, both fetched and rendered):

- **Suffix `A` = "Pin Out: 1 to 1"** — drawing GAM-286, title block reads
  "1.0mm Pitch SR Standard Catalog Assembly - 4" Overall Length - Pin Out: 1 to 1".
  The drawing shows PIN 1 marked on the **same (top) edge at both ends**.
  VERIFIED — https://gam-gec.com/wp-content/uploads/2018/10/GAM-286.pdf
- **Suffix `B` = "Pin Out: 1 to N"** — drawing GAM-287, same title but "Pin Out: 1 to N".
  Drawing shows PIN 1 on the top edge at the left end and on the **bottom edge** at the right end.
  VERIFIED — https://gam-gec.com/wp-content/uploads/2018/10/GAM-287.pdf

DigiKey's "Connector Type" attribute says the reverse of this:
- `A08SR08SR30K102A` → "Socket to Socket, **Reversed**" (VERIFIED, DigiKey 9922205)
- `A08SR08SR30K102B` → "Socket to Socket" (VERIFIED, DigiKey 9922206, DKPN 455-3656-ND)

Reconciliation (reasoned, not stated by either source — UNVERIFIED interpretation):
DigiKey is describing the **physical connector body orientation** (one housing flipped
relative to the other), JST is describing the **electrical net mapping**. With a flat
ribbon where all wires leave on one face, flipping one housing is exactly what produces
pin 1 → pin 1. The two statements are consistent once you read "Reversed" as "housing
flipped", not "pin-out reversed".

**Decision: order the `A` suffix for pin 1 → pin 1.** The JST drawing is the authoritative
statement and it is explicit. On DigiKey the `A` part will be listed as "Reversed" — expect
this and do not switch to `B` because of it.

Risk R1: if this interpretation is wrong, the `B` parts are the same price and in stock, so
buy one of each length for the first prototype build and buzz them out with a meter before
committing. Cost of hedging: about $2.

Both suffixes are physically identical otherwise: 30 AWG UL1571 black wire, 101.6 ±5.0 mm
wire length / 108.8 ±5.0 mm overall for the `102` size (VERIFIED, GAM-286/287).
Wire colour: **all black, no colour coding** — DigiKey colour attribute is
"Black, Individual" (VERIFIED). Pin 1 is identified by the housing marking only.

## F4. DigiKey availability and price (all VERIFIED, DigiKey keyword search pages, 2026-09-13)

### 8 position — USB harness (VBUS, VBUS, GND, D+, D−, GND, CC1, CC2)
| Part | Length | Price q1 | Stock |
|---|---|---|---|
| A08SR08SR30K102A | 101.6 mm (4") | $1.90 | 2,220 |
| A08SR08SR30K152A | 152.4 mm (6") | $2.08 | 1,181 |
| A08SR08SR30K102B | 101.6 mm | $1.90 | 706 |
| A08SR08SR30K152B | 152.4 mm | $2.08 | 79 |
| A08SR08SR30K51A | 50.8 mm | $1.78 | 2,084 |
| A08SR08SR30K203A | 203.2 mm | $2.25 | 288 |
| A08SR08SR30K254A | 254 mm | $2.46 | 963 |
| A08SR08SR30K305A | 304.8 mm | $2.83 | 784 |

Source: https://www.digikey.com/en/products/result?keywords=A08SR08SR
Price breaks for A08SR08SR30K102B: $1.615 @10, $1.372 @100, $1.166 @1000 (VERIFIED).

### 7 position — LED board
| Part | Length | Price q1 | Stock |
|---|---|---|---|
| A07SR07SR30K102A | 101.6 mm | $1.81 | 486 |
| A07SR07SR30K102B | 101.6 mm | $1.71 | 870 |
| A07SR07SR30K51A | 50.8 mm | $1.58 | 5,326 |
| A07SR07SR30K152B | 152.4 mm | $2.02 | 367 |
| A07SR07SR30K152A | 152.4 mm | $1.90 | **0** |
| A07SR07SR30K203B | 203.2 mm | $2.04 | 112 |
| A07SR07SR30K305A | 304.8 mm | $2.57 | 601 |
| A07SR07SR30K254A/B | 254 mm | $1.32 | **0** |

Source: https://www.digikey.com/en/products/result?keywords=A07SR07SR

### 4 position — PDM microphone
| Part | Length | Price q1 | Stock |
|---|---|---|---|
| A04SR04SR30K102A | 101.6 mm | $1.31 | **0** |
| A04SR04SR30K102B | 101.6 mm | $1.35 | **0** |
| A04SR04SR30K152A | 152.4 mm | $1.53 | 4,520 |
| A04SR04SR30K152B | 152.4 mm | $1.53 | 3,988 |
| A04SR04SR30K203A | 203.2 mm | $1.52 | 1,159 |
| A04SR04SR30K254A | 254 mm | $1.63 | 390 |
| A04SR04SR30K305A | 304.8 mm | $1.85 | 1,295 |

Source: https://www.digikey.com/en/products/result?keywords=A04SR04SR
**Both 100 mm 4-position parts are out of stock.** Use the 152 mm version, or use an
Adafruit STEMMA QT cable (F5) which is exactly 100 mm and cheaper.

### 2 position — optional
| Part | Length | Price q1 | Stock |
|---|---|---|---|
| A02SR02SR30K102A | 101.6 mm | $1.12 | 2,677 |
| A02SR02SR30K102B | 101.6 mm | $1.31 | **0** |
| A02SR02SR30K152A | 152.4 mm | $1.23 | 4,421 |
| A02SR02SR30K51A | 50.8 mm | $1.06 | 818 |

Source: https://www.digikey.com/en/products/result?keywords=A02SR02SR

DigiKey lead time on all of these is 8 weeks if ordered against non-stock (VERIFIED).
Mouser was not checked — UNVERIFIED.

## F5. 4-position alternative: Adafruit STEMMA QT / Qwiic

- **Adafruit 4210**, "STEMMA QT / Qwiic JST SH 4-pin Cable - 100mm Long", $0.95.
  "fitted with JST-SH female 4-pin connectors on both ends", 1 mm pitch.
  Wire colours red (3.3 V), black (GND), blue (SDA), yellow (SCL).
  Other lengths: 50 mm $0.95, 200 mm $1.25, 300 mm $1.25, 400 mm $1.50.
  VERIFIED — https://www.adafruit.com/product/4210
- Orientation: the Adafruit page describes the cable as symmetrical / pin-to-pin
  (the page's own wording is "The cables are made symmetrically so you don't worry about
  which side goes where"). Pin 1 → pin 1 is **UNVERIFIED** as an explicit datasheet
  statement; it is the Qwiic standard behaviour and every Qwiic board relies on it.
- Wire gauge: **UNVERIFIED**. Adafruit does not publish it. Qwiic cables are commonly 28 AWG
  (UNVERIFIED). The SH contact accepts AWG #32–#28, so either 28 or 30 AWG is in spec.
- SparkFun: PRT-14427 (Qwiic Cable 100mm, $1.50) is **retired and out of stock**; SparkFun
  points to PRT-17259 "Flexible Qwiic Cable - 100mm". VERIFIED for retirement/redirect at
  https://www.sparkfun.com/qwiic-cable-100mm.html ; PRT-17259 specs UNVERIFIED.
- Seeed Grove is 2.0 mm pitch, **not** SH — not usable. UNVERIFIED (search budget exhausted
  before confirming on seeedstudio.com); do not rely on this without a check.

Adafruit sells **no 7-pin or 8-pin JST SH double-ended cable** — a site product search for
"JST SH 8-pin cable" returns no products. VERIFIED —
https://www.adafruit.com/?q=JST+SH+8-pin+cable&post_type=product

## F6. Fallback: single-wire pre-crimped leads (VERIFIED, DigiKey)

### SH, 28 AWG, socket-to-socket, black
Source: https://www.digikey.com/en/products/result?keywords=ASSHSSH28K
| Part | Length | Price q1 | Stock |
|---|---|---|---|
| ASSHSSH28K51 | 50.8 mm | $0.46 | 19,911 |
| ASSHSSH28K102 | 101.6 mm | $0.49 | 16,348 |
| ASSHSSH28K152 | 152.4 mm | $0.49 | **0** |
| ASSHSSH28K203 | 203.2 mm | $0.50 | 8,332 |
| ASSHSSH28K254 | 254 mm | $0.57 | 8,402 |
| ASSHSSH28K305 | 304.8 mm | $0.56 | 8,716 |

Note the 152 mm length is out of stock; 102 and 203 are deep.
Loose housings: SHR-02V-S-B / SHR-04V-S-B / SHR-07V-S-B / SHR-08V-S-B, all listed in the
JST SH datasheet (VERIFIED, eSH.pdf; positions 2–16 and 20 exist).
SHR-08V-S-B is $0.17 q1, 25,206 in stock, DKPN 455-1383-ND (VERIFIED,
https://www.digikey.com/en/products/result?keywords=SHR-08V-S-B).

Cost of the 8-pin USB harness this way: 8 × $0.49 + 2 × $0.17 = $4.26, vs $1.90 ready-made.

### PH, 24 AWG, socket-to-socket, black
Source: https://www.digikey.com/en/products/result?keywords=ASPHSPH24K
| Part | Length | Price q1 | Stock |
|---|---|---|---|
| ASPHSPH24K51 | 50.8 mm | $0.37 | 16,197 |
| ASPHSPH24K102 | 101.6 mm | $0.40 | 15,724 |
| ASPHSPH24K152 | 152.4 mm | $0.40 | 37,430 |
| ASPHSPH24K203 | 203.2 mm | $0.44 | 2,422 |
| ASPHSPH24K254 | 254 mm | $0.47 | 7,163 |
| **ASPHSPH24K305** | 304.8 mm | $0.50 | **51,611** |

## F7. Other sources considered

- **DigiKey custom cable service** — DigiKey Guntersville does automated crimp and IDC
  terminations on JST connectors. Mentioned on
  https://www.digikey.com/en/product-highlight/j/jst/idc-assemblies-and-pre-crimped-leads
  (VERIFIED that the service exists). Pricing/MOQ/turnaround UNVERIFIED. Not needed — the
  catalog parts cover every position count required.
- **Amazon / AliExpress generic "JST SH 1.0mm 8-pin double-ended 10cm"** — not needed and
  not recommended. Generic listings frequently ship the reversed pin-out and rarely state
  which. If one is used anyway: photograph both ends with the latch/ramp face up; if the
  red (or pin-1-marked) wire sits on the same edge at both ends with both housings latch-up,
  the cable is reversed; if pin 1 is on opposite edges with both latch-up, it is 1-to-1.
  Always buzz it out. This paragraph is reasoning, UNVERIFIED against any listing.

## Recommendations

| Need | Part | Source | Price q1 | Stock | Pin-out |
|---|---|---|---|---|---|
| 8-pos USB, ~100 mm | A08SR08SR30K102A | DigiKey | $1.90 | 2,220 | 1→1 (listed as "Reversed") |
| 8-pos USB, ~150 mm | A08SR08SR30K152A | DigiKey | $2.08 | 1,181 | 1→1 |
| 7-pos LED, ~100 mm | A07SR07SR30K102A | DigiKey | $1.81 | 486 | 1→1 |
| 4-pos PDM mic, 100 mm | Adafruit 4210 | Adafruit | $0.95 | in stock | 1→1 (colour coded) |
| 4-pos PDM mic, alt | A04SR04SR30K152A (152 mm) | DigiKey | $1.53 | 4,520 | 1→1 |
| 2-pos, ~100 mm | A02SR02SR30K102A | DigiKey | $1.12 | 2,677 | 1→1 |

Buy one `B`-suffix part alongside the first order to settle R1 empirically.
